mainehackerclub/NameThatStyle/CMusic.cpp

#include "CMusic.h"

#define CMUSIC_STATE_PLAY 1
#define CMUSIC_STATE_STOP 0

CMusic::CMusic(byte apinPower, byte apinStandBy, byte apinMute) : 
  onFinishPlay(NULL), 
  state(CMUSIC_STATE_STOP), 
  pinPower(apinPower), 
  pinStandBy(apinStandBy), 
  pinMute(apinMute) 
{
  digitalWrite(this->pinPower, LOW);
  digitalWrite(this->pinStandBy, LOW);
  digitalWrite(this->pinMute, LOW);
  pinMode(this->pinPower, OUTPUT);
  pinMode(this->pinStandBy, OUTPUT);
  pinMode(this->pinMute, OUTPUT);

}

void CMusic::begin() {
  
}


void CMusic::update() {
  if (this->state == CMUSIC_STATE_PLAY) {
    if (this->getTimePlaying() >= this->duration) {
      this->stop();
      if (this->onFinishPlay != NULL) this->onFinishPlay();
    } 
  }
}

void CMusic::play(long aduration) {
  this->state = CMUSIC_STATE_PLAY;
  this->duration = aduration;
  this->timePlayStart = millis();
  digitalWrite(this->pinPower, HIGH); //power on mp3 player
  digitalWrite(this->pinStandBy, HIGH); //power on amplifier
  delay(500); //wait for amp to start to avoid poping noise
  digitalWrite(this->pinMute, HIGH); //unmute
}

void CMusic::stop() {
  this->state = CMUSIC_STATE_STOP;
  digitalWrite(this->pinMute, LOW); //mute
  delay(500); //wait for amp  to avoid poping noise
  digitalWrite(this->pinStandBy, LOW); //power off amp
  digitalWrite(this->pinPower, LOW); //power off mp3 player
}

byte CMusic::isPlaying() {
  return this->state;
}

long CMusic::getTimePlaying() {
  return millis() - this->timePlayStart;
}

//moo
